printicus/Klicky-Changer/Hardware/CAD/For MiniBurner XL Toolhead/Images/Backplate Miniburner XL 02.jpg

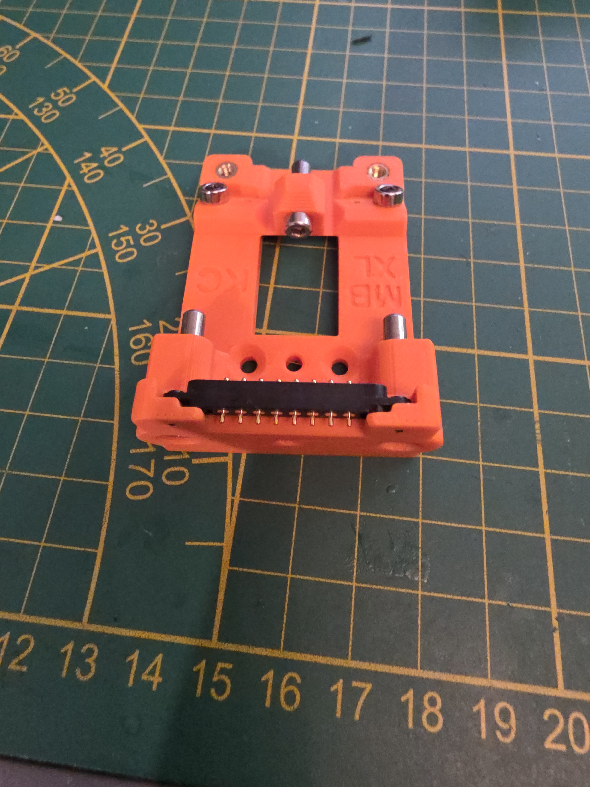
Hardware/CAD/For MiniBurner XL Toolhead/Images/Backplate Miniburner XL 02.jpg
