printicus/Klicky-Changer/Hardware/CAD/For MiniBurner XL Toolhead/Images/Dock_01.jpg

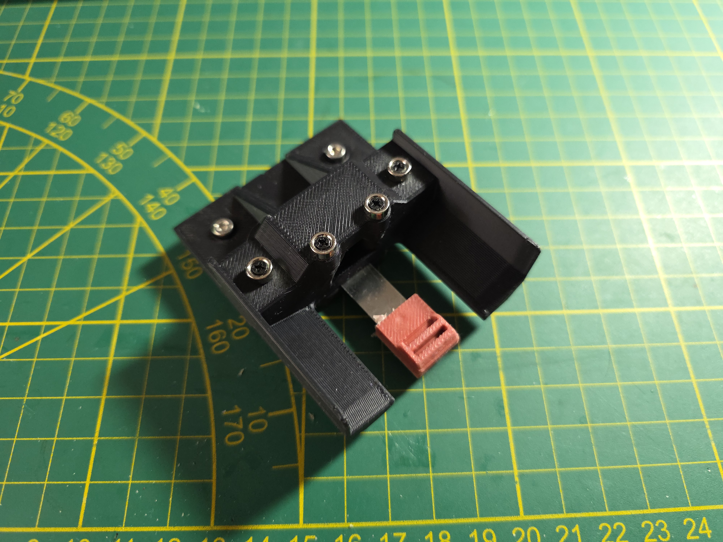
Hardware/CAD/For MiniBurner XL Toolhead/Images/Dock_01.jpg
