printicus/Klicky-Changer/Hardware/CAD/For MiniBurner XL Toolhead/Images/Dock_02.jpg

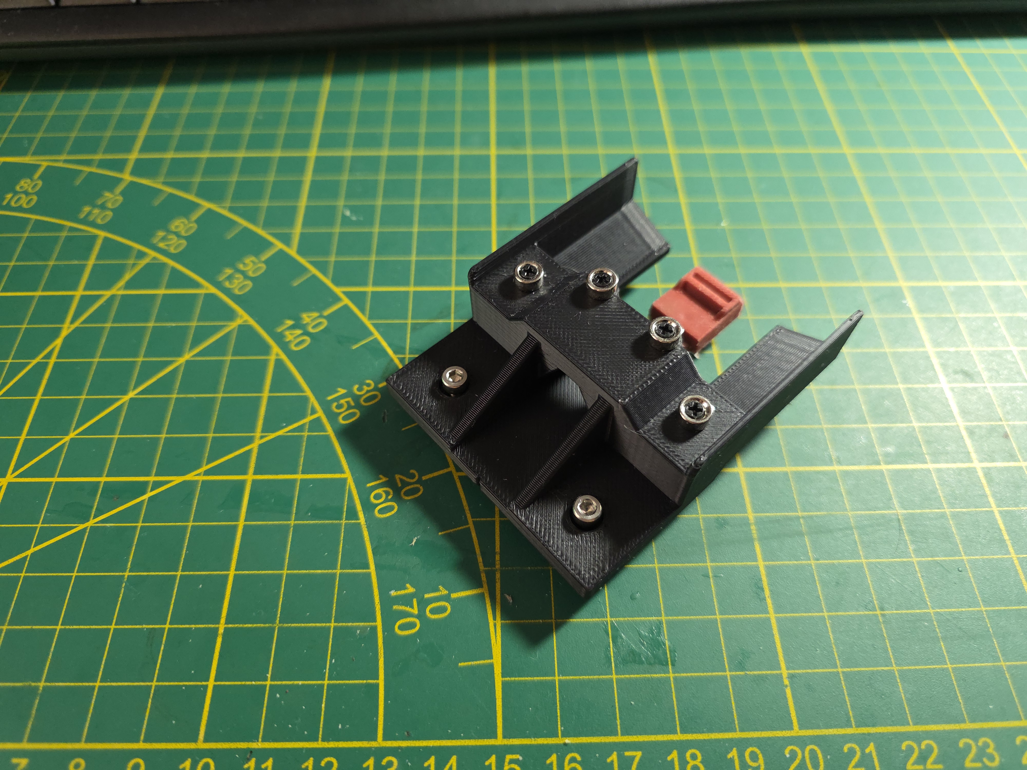
Hardware/CAD/For MiniBurner XL Toolhead/Images/Dock_02.jpg
