printicus/Klicky-Changer/Hardware/CAD/For MiniBurner XL Toolhead/Images/Dock_03.jpg

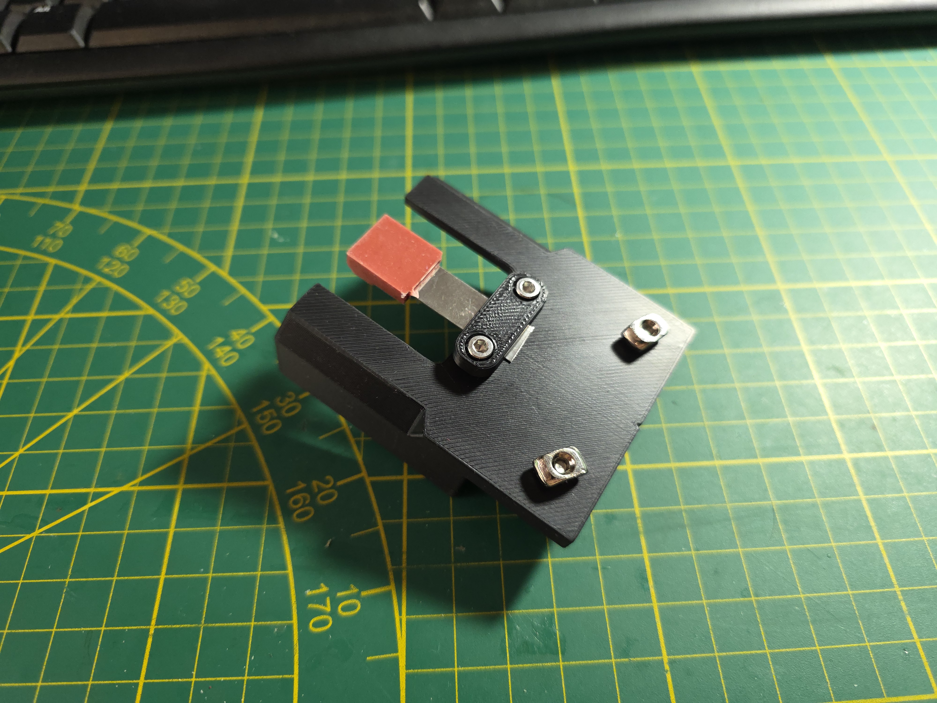
Hardware/CAD/For MiniBurner XL Toolhead/Images/Dock_03.jpg
