printicus/Klicky-Changer/Hardware/Images/Shuttle PCB Klicky 02.jpg

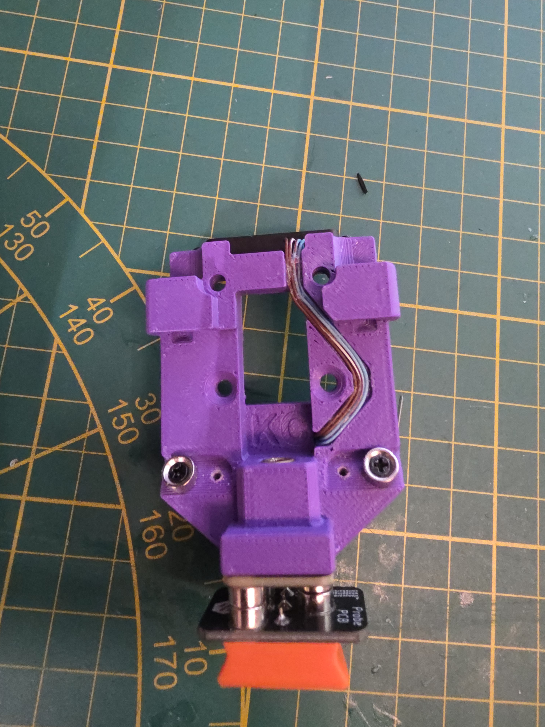
Hardware/Images/Shuttle PCB Klicky 02.jpg
