printicus/Klicky-Changer/Hardware/Images/Shuttle PCB Klicky 04.jpg

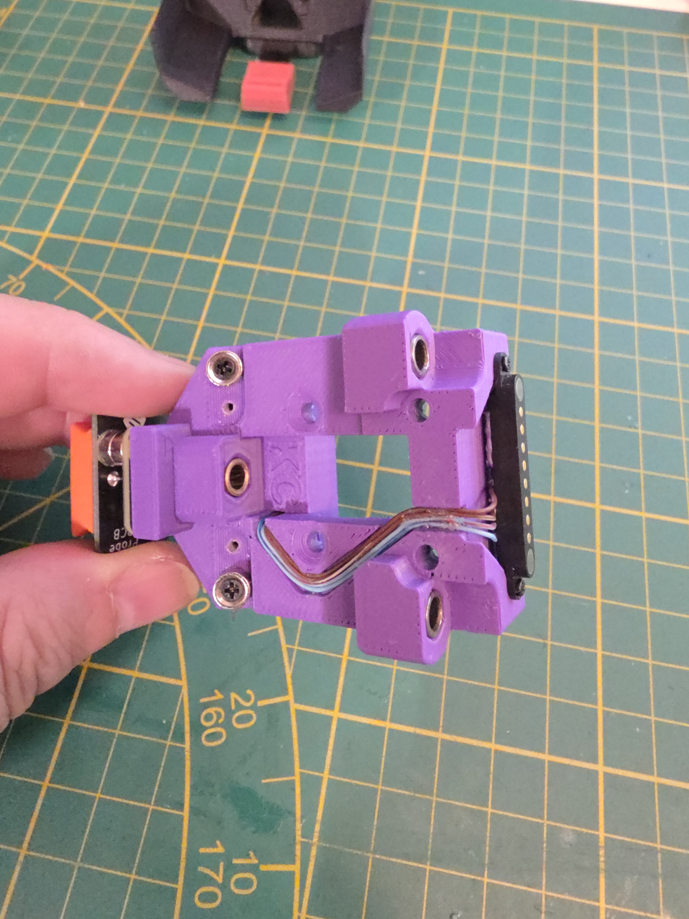
Hardware/Images/Shuttle PCB Klicky 04.jpg
