printicus/Klicky-Changer/Configs/Klipper-Toolchanger/toolchanger.cfg

[toolchanger]
  t_command_restore_axis: XYZ
  params_safe_y: 120
  params_close_y: 30
  params_fast_speed: 30000 # Go as fast as we can - the number represents mm/minute
  params_path_speed: 1500 # Speed for the actual change - the number represents mm/minute
  
  # Path positions relative to the park position
  # use x,y,z; f= multiplier to path speed; verify= Verify tool detected at end of the move.

  # CHANGE THIS!!! Set the path for your printer, see tool_paths.md
  params_dropoff_path: [{'z':0, 'y':0}, {'z':-10, 'y':0}]                          # dropoff path for MiniBurner XL
  #params_pickup_path: [{'z':-10, 'y':0}, {'z':0, 'y':0}]                          # pickup path for MiniBurner XL without "verify"
  #params_pickup_path: [{'z':-10, 'y':0}, {'z':0, 'y':0, 'f':0.5, 'verify':1}]     # pickup path for MiniBurner XL with "verify", half speed
  params_pickup_path: [{'z':-10, 'y':0}, {'z':0, 'y':0, 'verify':1}]               # pickup path for MiniBurner XL with "verify"

  # Default shaper params
  params_input_shaper_freq_x: 40.0
  params_input_shaper_freq_y: 40.0

  initialize_on: home                 # options: manual, home, first-use
  
  require_tool_present: False         # options: True, False
  
  abort_on_tool_missing: False         # options: True, False   - Works as a crash detection

  on_axis_not_homed: abort            # options: abort, home

  error_gcode:
    PAUSE

  before_change_gcode:
    {% set tn = "T"+(tool.tool_number|string) %}
    {% if printer["gcode_macro " + tn ] %}
       SET_GCODE_VARIABLE MACRO={tn} VARIABLE=color VALUE="''"
    {% endif %}

  after_change_gcode:
    {% set tn = "T"+(tool.tool_number|string) %}
    {% if printer["gcode_macro " + tn ] %}
       SET_GCODE_VARIABLE MACRO={tn} VARIABLE=color VALUE="'c44'"
    {% endif %}
    {% if tool.params_input_shaper_freq_x and tool.params_input_shaper_freq_y %}
          {% if tool.params_input_shaper_type_x and tool.params_input_shaper_type_y %}
            {% if tool.params_input_shaper_damping_ratio_x and tool.params_input_shaper_damping_ratio_y %}
              SET_INPUT_SHAPER SHAPER_FREQ_X={tool.params_input_shaper_freq_x} SHAPER_FREQ_Y={tool.params_input_shaper_freq_y} SHAPER_TYPE_X={tool.params_input_shaper_type_x} SHAPER_TYPE_Y={tool.params_input_shaper_type_y} DAMPING_RATIO_X={tool.params_input_shaper_damping_ratio_x} DAMPING_RATIO_Y={tool.params_input_shaper_damping_ratio_y}
            {% else %}
              SET_INPUT_SHAPER SHAPER_FREQ_X={tool.params_input_shaper_freq_x} SHAPER_FREQ_Y={tool.params_input_shaper_freq_y} SHAPER_TYPE_X={tool.params_input_shaper_type_x} SHAPER_TYPE_Y={tool.params_input_shaper_type_y} DAMPING_RATIO_X={params_input_shaper_damping_ratio_x} DAMPING_RATIO_Y={params_input_shaper_damping_ratio_y}
            {% endif %}
          {% else %}
            SET_INPUT_SHAPER SHAPER_FREQ_X={tool.params_input_shaper_freq_x} SHAPER_FREQ_Y={tool.params_input_shaper_freq_y} SHAPER_TYPE_X={params_input_shaper_type_x} SHAPER_TYPE_Y={params_input_shaper_type_y} DAMPING_RATIO_X={params_input_shaper_damping_ratio_x} DAMPING_RATIO_Y={params_input_shaper_damping_ratio_y}
          {% endif %}
        {% else %}
          SET_INPUT_SHAPER SHAPER_FREQ_X={params_input_shaper_freq_x} SHAPER_FREQ_Y={params_input_shaper_freq_y} SHAPER_TYPE_X={params_input_shaper_type_x} SHAPER_TYPE_Y={params_input_shaper_type_y} DAMPING_RATIO_X={params_input_shaper_damping_ratio_x} DAMPING_RATIO_Y={params_input_shaper_damping_ratio_y}
        {% endif %}

  dropoff_gcode:
    {% set x = tool.params_park_x|float %}
    {% set y = tool.params_park_y|float %}
    {% set z = tool.params_park_z|float %}
    {% set fast = tool.params_fast_speed|float %}
    {% set path = tool.params_dropoff_path %}
    {% set max_z = printer.configfile.config["stepper_z"]["position_max"]|float %}
    {% set cur_z = printer.toolhead.position[2]|float %}
    RESPOND TYPE=echo MSG='Dropping off {tool.name}'
    G90
    ; Move 1 mm up to avoid crashing into things
    G0 Z{ [cur_z+1.0, max_z]|min } F{fast}
    #   ##############  Move up to the dock  ##############
    ROUNDED_G0 Y={tool.params_safe_y} X={x} D=150 F={fast}
    ROUNDED_G0 Z={z + path[0]['z']|float} D=30 F={fast}
    ROUNDED_G0 Y={y + path[0]['y']|float} D=0 F={fast}
    #  ############## Run the path ##############
    {% for pos in path %}
      {% set speed = tool.params_path_speed|float * (pos.get('f', 1.0)|float) %}
      G0 {% if 'x' in pos %}X{x + pos['x']|float}{% endif %} {% if 'y' in pos %}Y{y + pos['y']|float}{% endif %} {% if 'z' in pos %}Z{z + pos['z']|float }{% endif %} F{speed}
    {% endfor %}
    
    {% if pickup_tool is none %}
#    G0 Y{tool.params_safe_y} F{fast}
#    G0 Z{restore_position.Z} F{fast} X{restore_position.X} F{fast} Y{restore_position.Y} F{fast}
    ROUNDED_G0 Y={tool.params_safe_y} F={fast} D=20
    ROUNDED_G0 Z={restore_position.Z} F={fast} D=150
    ROUNDED_G0 X={restore_position.X} Y={restore_position.Y} F={fast} D=0
    {% endif %}
    ROUNDED_G0 D=0

  pickup_gcode:
    {% set x = tool.params_park_x|float %}
    {% set y = tool.params_park_y|float %}
    {% set z = tool.params_park_z|float %}
    {% set fast = tool.params_fast_speed|float %}
    {% set path = tool.params_pickup_path %}
    RESPOND TYPE=echo MSG='Picking up {tool.name}'
    G90
    #   ##############  Fast to the last point  ##############
    {% if dropoff_tool is none and pickup_tool is not none %}
      ROUNDED_G0 Y={tool.params_safe_y} X={x} F={fast} D=150
      ROUNDED_G0 X={x} Z={z + path[0]['z']|float} F={fast} D=40
    {% else %}
      ROUNDED_G0 Y={tool.params_close_y} F={fast} D=5
      ROUNDED_G0 X={x} Z={z + path[0]['z']|float} F={fast} D=5
    {% endif %}
    
      ROUNDED_G0 Y={y + path[0]['y']|float} F={fast} D=0
      
    # Wait for temp before actually picking up the tool, while the nozzle is resting on it's pad.
    {% if tool.extruder %}
      M109 T{tool.tool_number} S{printer[tool.extruder].target|int}
    {% endif %}

    # Run the path
    {% for pos in path %}
      {% set speed = tool.params_path_speed|float * (pos.get('f', 1.0)|float) %}
      G0 {% if 'x' in pos %}X{x + pos['x']|float}{% endif %} {% if 'y' in pos %}Y{y + pos['y']|float}{% endif %} {% if 'z' in pos %}Z{z + pos['z']|float }{% endif %} F{speed}
      {% if 'verify' in pos %}
        M400
        VERIFY_TOOL_DETECTED T={tool.tool_number} ASYNC=1
      {% endif %}
    {% endfor %}
    # Restore the position with smooth rounded move.    
#    G0 Y{tool.params_safe_y} F{fast}
#    G0 Z{restore_position.Z+5} F{fast} X{restore_position.X} F{fast} Y{restore_position.Y} F{fast}
    ROUNDED_G0 Y={tool.params_safe_y} F={fast} D=20
    ROUNDED_G0 Z={restore_position.Z+5} F={fast} D=150
    ROUNDED_G0 X={restore_position.X} Y={restore_position.Y} F={fast} D=0
    ROUNDED_G0 Z={restore_position.Z} F={fast}
    ROUNDED_G0 D=0

[gcode_macro RESUME]
rename_existing: RESUME_BASE
gcode:
  INITIALIZE_TOOLCHANGER
  VERIFY_TOOL_DETECTED
  RESUME_BASE

[gcode_macro TOOL_ALIGN_START]
gcode:
    INITIALIZE_TOOLCHANGER # Detect current tool
    _TOOL_ALIGN_START

[gcode_macro _TOOL_ALIGN_START]
gcode:
    {% set tool = printer[printer.toolchanger.tool] %}
    SET_TOOL_PARAMETER PARAMETER='params_path_speed' VALUE=300
    ENTER_DOCKING_MODE
    G0 Y{tool.params_safe_y} F{tool.params_fast_speed}
    G0 X{tool.params_park_x} Z{tool.params_park_z}
    G0 Y{tool.params_park_y|float + 100.0}

[gcode_macro TOOL_ALIGN_TEST]
gcode:
    {% set curpos = printer.gcode_move.gcode_position %}
    {% if curpos[1] > 0 %}
      # Check if Y is not too far, to very unrealistic tests.
      RESPOND TYPE=error MSG='Test aborted. Tool too far away from the dock.'
    {% else %}
      SET_TOOL_PARAMETER PARAMETER='params_park_x' VALUE={curpos[0]}
      SET_TOOL_PARAMETER PARAMETER='params_park_y' VALUE={curpos[1]}
      SET_TOOL_PARAMETER PARAMETER='params_park_z' VALUE={curpos[2]}
      TEST_TOOL_DOCKING RESTORE_AXIS=XYZ
    {% endif %}

[gcode_macro TOOL_ALIGN_DONE]
gcode:
    {% set tool = printer[printer.toolchanger.tool] %}
    SAVE_TOOL_PARAMETER PARAMETER='params_park_x'
    SAVE_TOOL_PARAMETER PARAMETER='params_park_y'
    SAVE_TOOL_PARAMETER PARAMETER='params_park_z'
    RESET_TOOL_PARAMETER PARAMETER='params_path_speed'
    G0 Y{tool.params_safe_y} F{tool.params_fast_speed}
    EXIT_DOCKING_MODE
